vladisenko/EachiWhoop/photo/2.JPG

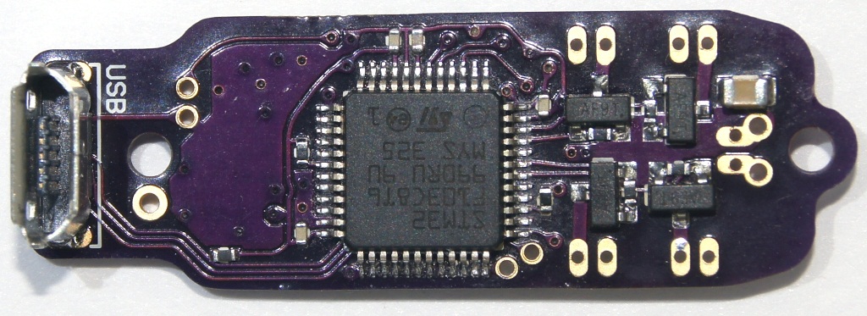
photo/2.JPG
