vladisenko/EachiWhoop/photo/3.JPG

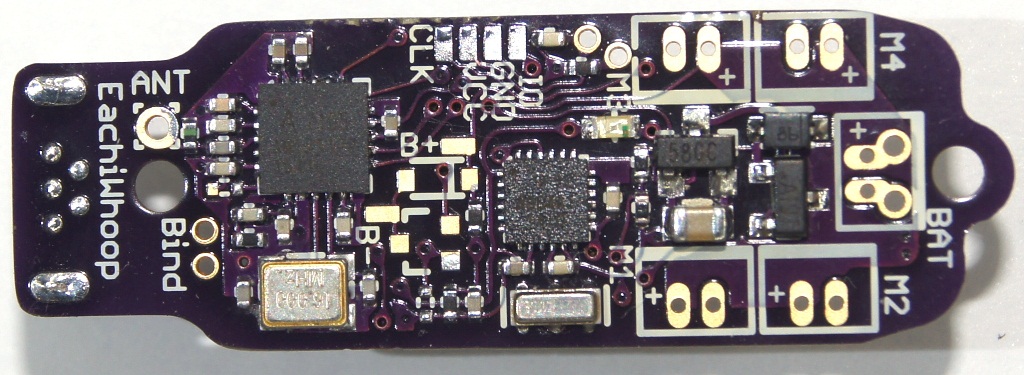
photo/3.JPG
