vladisenko/EachiWhoop/photo/4.JPG

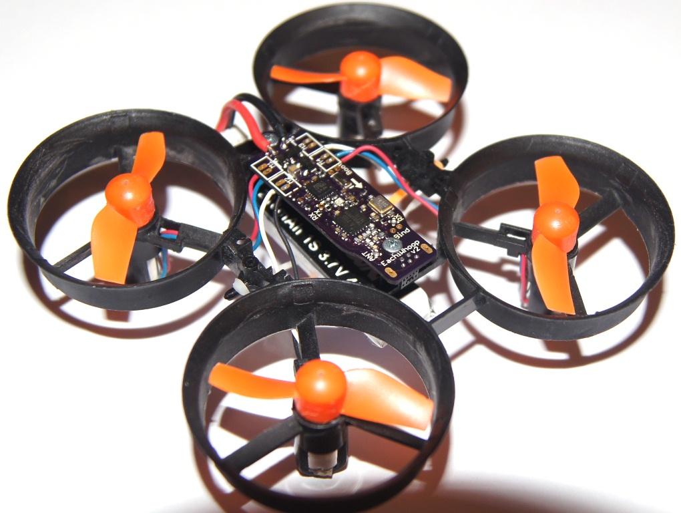
photo/4.JPG
