vladisenko/EachiWhoop/photo/5.JPG

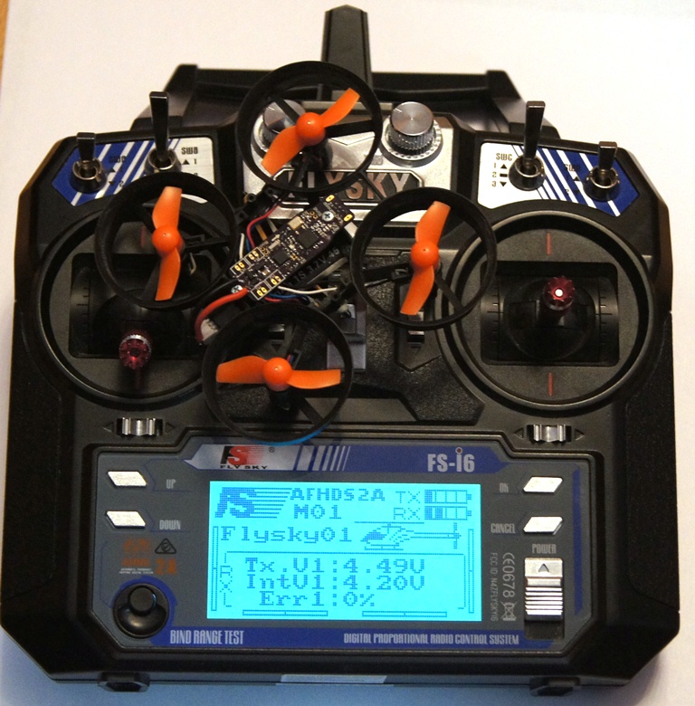
photo/5.JPG
